Seedmate/Seedmate/SW/src/words_opt.h

#ifndef WORDS_H
#define WORDS_H

const char bip39_words[] =
    "ABANDON\0ABILITY\0ABLE\0ABOUT\0ABOVE\0ABSENT\0ABSORB\0ABSTRACT\0"
    "ABSURD\0ABUSE\0ACCESS\0ACCIDENT\0ACCOUNT\0ACCUSE\0ACHIEVE\0ACID\0"
    "ACOUSTIC\0ACQUIRE\0ACROSS\0ACT\0ACTION\0ACTOR\0ACTRESS\0ACTUAL\0"
    "ADAPT\0ADD\0ADDICT\0ADDRESS\0ADJUST\0ADMIT\0ADULT\0ADVANCE\0"
    "ADVICE\0AEROBIC\0AFFAIR\0AFFORD\0AFRAID\0AGAIN\0AGE\0AGENT\0"
    "AGREE\0AHEAD\0AIM\0AIR\0AIRPORT\0AISLE\0ALARM\0ALBUM\0"
    "ALCOHOL\0ALERT\0ALIEN\0ALL\0ALLEY\0ALLOW\0ALMOST\0ALONE\0"
    "ALPHA\0ALREADY\0ALSO\0ALTER\0ALWAYS\0AMATEUR\0AMAZING\0AMONG\0"
    "AMOUNT\0AMUSED\0ANALYST\0ANCHOR\0ANCIENT\0ANGER\0ANGLE\0ANGRY\0"
    "ANIMAL\0ANKLE\0ANNOUNCE\0ANNUAL\0ANOTHER\0ANSWER\0ANTENNA\0ANTIQUE\0"
    "ANXIETY\0ANY\0APART\0APOLOGY\0APPEAR\0APPLE\0APPROVE\0APRIL\0"
    "ARCH\0ARCTIC\0AREA\0ARENA\0ARGUE\0ARM\0ARMED\0ARMOR\0"
    "ARMY\0AROUND\0ARRANGE\0ARREST\0ARRIVE\0ARROW\0ART\0ARTEFACT\0"
    "ARTIST\0ARTWORK\0ASK\0ASPECT\0ASSAULT\0ASSET\0ASSIST\0ASSUME\0"
    "ASTHMA\0ATHLETE\0ATOM\0ATTACK\0ATTEND\0ATTITUDE\0ATTRACT\0AUCTION\0"
    "AUDIT\0AUGUST\0AUNT\0AUTHOR\0AUTO\0AUTUMN\0AVERAGE\0AVOCADO\0"
    "AVOID\0AWAKE\0AWARE\0AWAY\0AWESOME\0AWFUL\0AWKWARD\0AXIS\0"
    "BABY\0BACHELOR\0BACON\0BADGE\0BAG\0BALANCE\0BALCONY\0BALL\0"
    "BAMBOO\0BANANA\0BANNER\0BAR\0BARELY\0BARGAIN\0BARREL\0BASE\0"
    "BASIC\0BASKET\0BATTLE\0BEACH\0BEAN\0BEAUTY\0BECAUSE\0BECOME\0"
    "BEEF\0BEFORE\0BEGIN\0BEHAVE\0BEHIND\0BELIEVE\0BELOW\0BELT\0"
    "BENCH\0BENEFIT\0BEST\0BETRAY\0BETTER\0BETWEEN\0BEYOND\0BICYCLE\0"
    "BID\0BIKE\0BIND\0BIOLOGY\0BIRD\0BIRTH\0BITTER\0BLACK\0"
    "BLADE\0BLAME\0BLANKET\0BLAST\0BLEAK\0BLESS\0BLIND\0BLOOD\0"
    "BLOSSOM\0BLOUSE\0BLUE\0BLUR\0BLUSH\0BOARD\0BOAT\0BODY\0"
    "BOIL\0BOMB\0BONE\0BONUS\0BOOK\0BOOST\0BORDER\0BORING\0"
    "BORROW\0BOSS\0BOTTOM\0BOUNCE\0BOX\0BOY\0BRACKET\0BRAIN\0"
    "BRAND\0BRASS\0BRAVE\0BREAD\0BREEZE\0BRICK\0BRIDGE\0BRIEF\0"
    "BRIGHT\0BRING\0BRISK\0BROCCOLI\0BROKEN\0BRONZE\0BROOM\0BROTHER\0"
    "BROWN\0BRUSH\0BUBBLE\0BUDDY\0BUDGET\0BUFFALO\0BUILD\0BULB\0"
    "BULK\0BULLET\0BUNDLE\0BUNKER\0BURDEN\0BURGER\0BURST\0BUS\0"
    "BUSINESS\0BUSY\0BUTTER\0BUYER\0BUZZ\0CABBAGE\0CABIN\0CABLE\0"
    "CACTUS\0CAGE\0CAKE\0CALL\0CALM\0CAMERA\0CAMP\0CAN\0"
    "CANAL\0CANCEL\0CANDY\0CANNON\0CANOE\0CANVAS\0CANYON\0CAPABLE\0"
    "CAPITAL\0CAPTAIN\0CAR\0CARBON\0CARD\0CARGO\0CARPET\0CARRY\0"
    "CART\0CASE\0CASH\0CASINO\0CASTLE\0CASUAL\0CAT\0CATALOG\0"
    "CATCH\0CATEGORY\0CATTLE\0CAUGHT\0CAUSE\0CAUTION\0CAVE\0CEILING\0"
    "CELERY\0CEMENT\0CENSUS\0CENTURY\0CEREAL\0CERTAIN\0CHAIR\0CHALK\0"
    "CHAMPION\0CHANGE\0CHAOS\0CHAPTER\0CHARGE\0CHASE\0CHAT\0CHEAP\0"
    "CHECK\0CHEESE\0CHEF\0CHERRY\0CHEST\0CHICKEN\0CHIEF\0CHILD\0"
    "CHIMNEY\0CHOICE\0CHOOSE\0CHRONIC\0CHUCKLE\0CHUNK\0CHURN\0CIGAR\0"
    "CINNAMON\0CIRCLE\0CITIZEN\0CITY\0CIVIL\0CLAIM\0CLAP\0CLARIFY\0"
    "CLAW\0CLAY\0CLEAN\0CLERK\0CLEVER\0CLICK\0CLIENT\0CLIFF\0"
    "CLIMB\0CLINIC\0CLIP\0CLOCK\0CLOG\0CLOSE\0CLOTH\0CLOUD\0"
    "CLOWN\0CLUB\0CLUMP\0CLUSTER\0CLUTCH\0COACH\0COAST\0COCONUT\0"
    "CODE\0COFFEE\0COIL\0COIN\0COLLECT\0COLOR\0COLUMN\0COMBINE\0"
    "COME\0COMFORT\0COMIC\0COMMON\0COMPANY\0CONCERT\0CONDUCT\0CONFIRM\0"
    "CONGRESS\0CONNECT\0CONSIDER\0CONTROL\0CONVINCE\0COOK\0COOL\0COPPER\0"
    "COPY\0CORAL\0CORE\0CORN\0CORRECT\0COST\0COTTON\0COUCH\0"
    "COUNTRY\0COUPLE\0COURSE\0COUSIN\0COVER\0COYOTE\0CRACK\0CRADLE\0"
    "CRAFT\0CRAM\0CRANE\0CRASH\0CRATER\0CRAWL\0CRAZY\0CREAM\0"
    "CREDIT\0CREEK\0CREW\0CRICKET\0CRIME\0CRISP\0CRITIC\0CROP\0"
    "CROSS\0CROUCH\0CROWD\0CRUCIAL\0CRUEL\0CRUISE\0CRUMBLE\0CRUNCH\0"
    "CRUSH\0CRY\0CRYSTAL\0CUBE\0CULTURE\0CUP\0CUPBOARD\0CURIOUS\0"
    "CURRENT\0CURTAIN\0CURVE\0CUSHION\0CUSTOM\0CUTE\0CYCLE\0DAD\0"
    "DAMAGE\0DAMP\0DANCE\0DANGER\0DARING\0DASH\0DAUGHTER\0DAWN\0"
    "DAY\0DEAL\0DEBATE\0DEBRIS\0DECADE\0DECEMBER\0DECIDE\0DECLINE\0"
    "DECORATE\0DECREASE\0DEER\0DEFENSE\0DEFINE\0DEFY\0DEGREE\0DELAY\0"
    "DELIVER\0DEMAND\0DEMISE\0DENIAL\0DENTIST\0DENY\0DEPART\0DEPEND\0"
    "DEPOSIT\0DEPTH\0DEPUTY\0DERIVE\0DESCRIBE\0DESERT\0DESIGN\0DESK\0"
    "DESPAIR\0DESTROY\0DETAIL\0DETECT\0DEVELOP\0DEVICE\0DEVOTE\0DIAGRAM\0"
    "DIAL\0DIAMOND\0DIARY\0DICE\0DIESEL\0DIET\0DIFFER\0DIGITAL\0"
    "DIGNITY\0DILEMMA\0DINNER\0DINOSAUR\0DIRECT\0DIRT\0DISAGREE\0DISCOVER\0"
    "DISEASE\0DISH\0DISMISS\0DISORDER\0DISPLAY\0DISTANCE\0DIVERT\0DIVIDE\0"
    "DIVORCE\0DIZZY\0DOCTOR\0DOCUMENT\0DOG\0DOLL\0DOLPHIN\0DOMAIN\0"
    "DONATE\0DONKEY\0DONOR\0DOOR\0DOSE\0DOUBLE\0DOVE\0DRAFT\0"
    "DRAGON\0DRAMA\0DRASTIC\0DRAW\0DREAM\0DRESS\0DRIFT\0DRILL\0"
    "DRINK\0DRIP\0DRIVE\0DROP\0DRUM\0DRY\0DUCK\0DUMB\0"
    "DUNE\0DURING\0DUST\0DUTCH\0DUTY\0DWARF\0DYNAMIC\0EAGER\0"
    "EAGLE\0EARLY\0EARN\0EARTH\0EASILY\0EAST\0EASY\0ECHO\0"
    "ECOLOGY\0ECONOMY\0EDGE\0EDIT\0EDUCATE\0EFFORT\0EGG\0EIGHT\0"
    "EITHER\0ELBOW\0ELDER\0ELECTRIC\0ELEGANT\0ELEMENT\0ELEPHANT\0ELEVATOR\0"
    "ELITE\0ELSE\0EMBARK\0EMBODY\0EMBRACE\0EMERGE\0EMOTION\0EMPLOY\0"
    "EMPOWER\0EMPTY\0ENABLE\0ENACT\0END\0ENDLESS\0ENDORSE\0ENEMY\0"
    "ENERGY\0ENFORCE\0ENGAGE\0ENGINE\0ENHANCE\0ENJOY\0ENLIST\0ENOUGH\0"
    "ENRICH\0ENROLL\0ENSURE\0ENTER\0ENTIRE\0ENTRY\0ENVELOPE\0EPISODE\0"
    "EQUAL\0EQUIP\0ERA\0ERASE\0ERODE\0EROSION\0ERROR\0ERUPT\0"
    "ESCAPE\0ESSAY\0ESSENCE\0ESTATE\0ETERNAL\0ETHICS\0EVIDENCE\0EVIL\0"
    "EVOKE\0EVOLVE\0EXACT\0EXAMPLE\0EXCESS\0EXCHANGE\0EXCITE\0EXCLUDE\0"
    "EXCUSE\0EXECUTE\0EXERCISE\0EXHAUST\0EXHIBIT\0EXILE\0EXIST\0EXIT\0"
    "EXOTIC\0EXPAND\0EXPECT\0EXPIRE\0EXPLAIN\0EXPOSE\0EXPRESS\0EXTEND\0"
    "EXTRA\0EYE\0EYEBROW\0FABRIC\0FACE\0FACULTY\0FADE\0FAINT\0"
    "FAITH\0FALL\0FALSE\0FAME\0FAMILY\0FAMOUS\0FAN\0FANCY\0"
    "FANTASY\0FARM\0FASHION\0FAT\0FATAL\0FATHER\0FATIGUE\0FAULT\0"
    "FAVORITE\0FEATURE\0FEBRUARY\0FEDERAL\0FEE\0FEED\0FEEL\0FEMALE\0"
    "FENCE\0FESTIVAL\0FETCH\0FEVER\0FEW\0FIBER\0FICTION\0FIELD\0"
    "FIGURE\0FILE\0FILM\0FILTER\0FINAL\0FIND\0FINE\0FINGER\0"
    "FINISH\0FIRE\0FIRM\0FIRST\0FISCAL\0FISH\0FIT\0FITNESS\0"
    "FIX\0FLAG\0FLAME\0FLASH\0FLAT\0FLAVOR\0FLEE\0FLIGHT\0"
    "FLIP\0FLOAT\0FLOCK\0FLOOR\0FLOWER\0FLUID\0FLUSH\0FLY\0"
    "FOAM\0FOCUS\0FOG\0FOIL\0FOLD\0FOLLOW\0FOOD\0FOOT\0"
    "FORCE\0FOREST\0FORGET\0FORK\0FORTUNE\0FORUM\0FORWARD\0FOSSIL\0"
    "FOSTER\0FOUND\0FOX\0FRAGILE\0FRAME\0FREQUENT\0FRESH\0FRIEND\0"
    "FRINGE\0FROG\0FRONT\0FROST\0FROWN\0FROZEN\0FRUIT\0FUEL\0"
    "FUN\0FUNNY\0FURNACE\0FURY\0FUTURE\0GADGET\0GAIN\0GALAXY\0"
    "GALLERY\0GAME\0GAP\0GARAGE\0GARBAGE\0GARDEN\0GARLIC\0GARMENT\0"
    "GAS\0GASP\0GATE\0GATHER\0GAUGE\0GAZE\0GENERAL\0GENIUS\0"
    "GENRE\0GENTLE\0GENUINE\0GESTURE\0GHOST\0GIANT\0GIFT\0GIGGLE\0"
    "GINGER\0GIRAFFE\0GIRL\0GIVE\0GLAD\0GLANCE\0GLARE\0GLASS\0"
    "GLIDE\0GLIMPSE\0GLOBE\0GLOOM\0GLORY\0GLOVE\0GLOW\0GLUE\0"
    "GOAT\0GODDESS\0GOLD\0GOOD\0GOOSE\0GORILLA\0GOSPEL\0GOSSIP\0"
    "GOVERN\0GOWN\0GRAB\0GRACE\0GRAIN\0GRANT\0GRAPE\0GRASS\0"
    "GRAVITY\0GREAT\0GREEN\0GRID\0GRIEF\0GRIT\0GROCERY\0GROUP\0"
    "GROW\0GRUNT\0GUARD\0GUESS\0GUIDE\0GUILT\0GUITAR\0GUN\0"
    "GYM\0HABIT\0HAIR\0HALF\0HAMMER\0HAMSTER\0HAND\0HAPPY\0"
    "HARBOR\0HARD\0HARSH\0HARVEST\0HAT\0HAVE\0HAWK\0HAZARD\0"
    "HEAD\0HEALTH\0HEART\0HEAVY\0HEDGEHOG\0HEIGHT\0HELLO\0HELMET\0"
    "HELP\0HEN\0HERO\0HIDDEN\0HIGH\0HILL\0HINT\0HIP\0"
    "HIRE\0HISTORY\0HOBBY\0HOCKEY\0HOLD\0HOLE\0HOLIDAY\0HOLLOW\0"
    "HOME\0HONEY\0HOOD\0HOPE\0HORN\0HORROR\0HORSE\0HOSPITAL\0"
    "HOST\0HOTEL\0HOUR\0HOVER\0HUB\0HUGE\0HUMAN\0HUMBLE\0"
    "HUMOR\0HUNDRED\0HUNGRY\0HUNT\0HURDLE\0HURRY\0HURT\0HUSBAND\0"
    "HYBRID\0ICE\0ICON\0IDEA\0IDENTIFY\0IDLE\0IGNORE\0ILL\0"
    "ILLEGAL\0ILLNESS\0IMAGE\0IMITATE\0IMMENSE\0IMMUNE\0IMPACT\0IMPOSE\0"
    "IMPROVE\0IMPULSE\0INCH\0INCLUDE\0INCOME\0INCREASE\0INDEX\0INDICATE\0"
    "INDOOR\0INDUSTRY\0INFANT\0INFLICT\0INFORM\0INHALE\0INHERIT\0INITIAL\0"
    "INJECT\0INJURY\0INMATE\0INNER\0INNOCENT\0INPUT\0INQUIRY\0INSANE\0"
    "INSECT\0INSIDE\0INSPIRE\0INSTALL\0INTACT\0INTEREST\0INTO\0INVEST\0"
    "INVITE\0INVOLVE\0IRON\0ISLAND\0ISOLATE\0ISSUE\0ITEM\0IVORY\0"
    "JACKET\0JAGUAR\0JAR\0JAZZ\0JEALOUS\0JEANS\0JELLY\0JEWEL\0"
    "JOB\0JOIN\0JOKE\0JOURNEY\0JOY\0JUDGE\0JUICE\0JUMP\0"
    "JUNGLE\0JUNIOR\0JUNK\0JUST\0KANGAROO\0KEEN\0KEEP\0KETCHUP\0"
    "KEY\0KICK\0KID\0KIDNEY\0KIND\0KINGDOM\0KISS\0KIT\0"
    "KITCHEN\0KITE\0KITTEN\0KIWI\0KNEE\0KNIFE\0KNOCK\0KNOW\0"
    "LAB\0LABEL\0LABOR\0LADDER\0LADY\0LAKE\0LAMP\0LANGUAGE\0"
    "LAPTOP\0LARGE\0LATER\0LATIN\0LAUGH\0LAUNDRY\0LAVA\0LAW\0"
    "LAWN\0LAWSUIT\0LAYER\0LAZY\0LEADER\0LEAF\0LEARN\0LEAVE\0"
    "LECTURE\0LEFT\0LEG\0LEGAL\0LEGEND\0LEISURE\0LEMON\0LEND\0"
    "LENGTH\0LENS\0LEOPARD\0LESSON\0LETTER\0LEVEL\0LIAR\0LIBERTY\0"
    "LIBRARY\0LICENSE\0LIFE\0LIFT\0LIGHT\0LIKE\0LIMB\0LIMIT\0"
    "LINK\0LION\0LIQUID\0LIST\0LITTLE\0LIVE\0LIZARD\0LOAD\0"
    "LOAN\0LOBSTER\0LOCAL\0LOCK\0LOGIC\0LONELY\0LONG\0LOOP\0"
    "LOTTERY\0LOUD\0LOUNGE\0LOVE\0LOYAL\0LUCKY\0LUGGAGE\0LUMBER\0"
    "LUNAR\0LUNCH\0LUXURY\0LYRICS\0MACHINE\0MAD\0MAGIC\0MAGNET\0"
    "MAID\0MAIL\0MAIN\0MAJOR\0MAKE\0MAMMAL\0MAN\0MANAGE\0"
    "MANDATE\0MANGO\0MANSION\0MANUAL\0MAPLE\0MARBLE\0MARCH\0MARGIN\0"
    "MARINE\0MARKET\0MARRIAGE\0MASK\0MASS\0MASTER\0MATCH\0MATERIAL\0"
    "MATH\0MATRIX\0MATTER\0MAXIMUM\0MAZE\0MEADOW\0MEAN\0MEASURE\0"
    "MEAT\0MECHANIC\0MEDAL\0MEDIA\0MELODY\0MELT\0MEMBER\0MEMORY\0"
    "MENTION\0MENU\0MERCY\0MERGE\0MERIT\0MERRY\0MESH\0MESSAGE\0"
    "METAL\0METHOD\0MIDDLE\0MIDNIGHT\0MILK\0MILLION\0MIMIC\0MIND\0"
    "MINIMUM\0MINOR\0MINUTE\0MIRACLE\0MIRROR\0MISERY\0MISS\0MISTAKE\0"
    "MIX\0MIXED\0MIXTURE\0MOBILE\0MODEL\0MODIFY\0MOM\0MOMENT\0"
    "MONITOR\0MONKEY\0MONSTER\0MONTH\0MOON\0MORAL\0MORE\0MORNING\0"
    "MOSQUITO\0MOTHER\0MOTION\0MOTOR\0MOUNTAIN\0MOUSE\0MOVE\0MOVIE\0"
    "MUCH\0MUFFIN\0MULE\0MULTIPLY\0MUSCLE\0MUSEUM\0MUSHROOM\0MUSIC\0"
    "MUST\0MUTUAL\0MYSELF\0MYSTERY\0MYTH\0NAIVE\0NAME\0NAPKIN\0"
    "NARROW\0NASTY\0NATION\0NATURE\0NEAR\0NECK\0NEED\0NEGATIVE\0"
    "NEGLECT\0NEITHER\0NEPHEW\0NERVE\0NEST\0NET\0NETWORK\0NEUTRAL\0"
    "NEVER\0NEWS\0NEXT\0NICE\0NIGHT\0NOBLE\0NOISE\0NOMINEE\0"
    "NOODLE\0NORMAL\0NORTH\0NOSE\0NOTABLE\0NOTE\0NOTHING\0NOTICE\0"
    "NOVEL\0NOW\0NUCLEAR\0NUMBER\0NURSE\0NUT\0OAK\0OBEY\0"
    "OBJECT\0OBLIGE\0OBSCURE\0OBSERVE\0OBTAIN\0OBVIOUS\0OCCUR\0OCEAN\0"
    "OCTOBER\0ODOR\0OFF\0OFFER\0OFFICE\0OFTEN\0OIL\0OKAY\0"
    "OLD\0OLIVE\0OLYMPIC\0OMIT\0ONCE\0ONE\0ONION\0ONLINE\0"
    "ONLY\0OPEN\0OPERA\0OPINION\0OPPOSE\0OPTION\0ORANGE\0ORBIT\0"
    "ORCHARD\0ORDER\0ORDINARY\0ORGAN\0ORIENT\0ORIGINAL\0ORPHAN\0OSTRICH\0"
    "OTHER\0OUTDOOR\0OUTER\0OUTPUT\0OUTSIDE\0OVAL\0OVEN\0OVER\0"
    "OWN\0OWNER\0OXYGEN\0OYSTER\0OZONE\0PACT\0PADDLE\0PAGE\0"
    "PAIR\0PALACE\0PALM\0PANDA\0PANEL\0PANIC\0PANTHER\0PAPER\0"
    "PARADE\0PARENT\0PARK\0PARROT\0PARTY\0PASS\0PATCH\0PATH\0"
    "PATIENT\0PATROL\0PATTERN\0PAUSE\0PAVE\0PAYMENT\0PEACE\0PEANUT\0"
    "PEAR\0PEASANT\0PELICAN\0PEN\0PENALTY\0PENCIL\0PEOPLE\0PEPPER\0"
    "PERFECT\0PERMIT\0PERSON\0PET\0PHONE\0PHOTO\0PHRASE\0PHYSICAL\0"
    "PIANO\0PICNIC\0PICTURE\0PIECE\0PIG\0PIGEON\0PILL\0PILOT\0"
    "PINK\0PIONEER\0PIPE\0PISTOL\0PITCH\0PIZZA\0PLACE\0PLANET\0"
    "PLASTIC\0PLATE\0PLAY\0PLEASE\0PLEDGE\0PLUCK\0PLUG\0PLUNGE\0"
    "POEM\0POET\0POINT\0POLAR\0POLE\0POLICE\0POND\0PONY\0"
    "POOL\0POPULAR\0PORTION\0POSITION\0POSSIBLE\0POST\0POTATO\0POTTERY\0"
    "POVERTY\0POWDER\0POWER\0PRACTICE\0PRAISE\0PREDICT\0PREFER\0PREPARE\0"
    "PRESENT\0PRETTY\0PREVENT\0PRICE\0PRIDE\0PRIMARY\0PRINT\0PRIORITY\0"
    "PRISON\0PRIVATE\0PRIZE\0PROBLEM\0PROCESS\0PRODUCE\0PROFIT\0PROGRAM\0"
    "PROJECT\0PROMOTE\0PROOF\0PROPERTY\0PROSPER\0PROTECT\0PROUD\0PROVIDE\0"
    "PUBLIC\0PUDDING\0PULL\0PULP\0PULSE\0PUMPKIN\0PUNCH\0PUPIL\0"
    "PUPPY\0PURCHASE\0PURITY\0PURPOSE\0PURSE\0PUSH\0PUT\0PUZZLE\0"
    "PYRAMID\0QUALITY\0QUANTUM\0QUARTER\0QUESTION\0QUICK\0QUIT\0QUIZ\0"
    "QUOTE\0RABBIT\0RACCOON\0RACE\0RACK\0RADAR\0RADIO\0RAIL\0"
    "RAIN\0RAISE\0RALLY\0RAMP\0RANCH\0RANDOM\0RANGE\0RAPID\0"
    "RARE\0RATE\0RATHER\0RAVEN\0RAW\0RAZOR\0READY\0REAL\0"
    "REASON\0REBEL\0REBUILD\0RECALL\0RECEIVE\0RECIPE\0RECORD\0RECYCLE\0"
    "REDUCE\0REFLECT\0REFORM\0REFUSE\0REGION\0REGRET\0REGULAR\0REJECT\0"
    "RELAX\0RELEASE\0RELIEF\0RELY\0REMAIN\0REMEMBER\0REMIND\0REMOVE\0"
    "RENDER\0RENEW\0RENT\0REOPEN\0REPAIR\0REPEAT\0REPLACE\0REPORT\0"
    "REQUIRE\0RESCUE\0RESEMBLE\0RESIST\0RESOURCE\0RESPONSE\0RESULT\0RETIRE\0"
    "RETREAT\0RETURN\0REUNION\0REVEAL\0REVIEW\0REWARD\0RHYTHM\0RIB\0"
    "RIBBON\0RICE\0RICH\0RIDE\0RIDGE\0RIFLE\0RIGHT\0RIGID\0"
    "RING\0RIOT\0RIPPLE\0RISK\0RITUAL\0RIVAL\0RIVER\0ROAD\0"
    "ROAST\0ROBOT\0ROBUST\0ROCKET\0ROMANCE\0ROOF\0ROOKIE\0ROOM\0"
    "ROSE\0ROTATE\0ROUGH\0ROUND\0ROUTE\0ROYAL\0RUBBER\0RUDE\0"
    "RUG\0RULE\0RUN\0RUNWAY\0RURAL\0SAD\0SADDLE\0SADNESS\0"
    "SAFE\0SAIL\0SALAD\0SALMON\0SALON\0SALT\0SALUTE\0SAME\0"
    "SAMPLE\0SAND\0SATISFY\0SATOSHI\0SAUCE\0SAUSAGE\0SAVE\0SAY\0"
    "SCALE\0SCAN\0SCARE\0SCATTER\0SCENE\0SCHEME\0SCHOOL\0SCIENCE\0"
    "SCISSORS\0SCORPION\0SCOUT\0SCRAP\0SCREEN\0SCRIPT\0SCRUB\0SEA\0"
    "SEARCH\0SEASON\0SEAT\0SECOND\0SECRET\0SECTION\0SECURITY\0SEED\0"
    "SEEK\0SEGMENT\0SELECT\0SELL\0SEMINAR\0SENIOR\0SENSE\0SENTENCE\0"
    "SERIES\0SERVICE\0SESSION\0SETTLE\0SETUP\0SEVEN\0SHADOW\0SHAFT\0"
    "SHALLOW\0SHARE\0SHED\0SHELL\0SHERIFF\0SHIELD\0SHIFT\0SHINE\0"
    "SHIP\0SHIVER\0SHOCK\0SHOE\0SHOOT\0SHOP\0SHORT\0SHOULDER\0"
    "SHOVE\0SHRIMP\0SHRUG\0SHUFFLE\0SHY\0SIBLING\0SICK\0SIDE\0"
    "SIEGE\0SIGHT\0SIGN\0SILENT\0SILK\0SILLY\0SILVER\0SIMILAR\0"
    "SIMPLE\0SINCE\0SING\0SIREN\0SISTER\0SITUATE\0SIX\0SIZE\0"
    "SKATE\0SKETCH\0SKI\0SKILL\0SKIN\0SKIRT\0SKULL\0SLAB\0"
    "SLAM\0SLEEP\0SLENDER\0SLICE\0SLIDE\0SLIGHT\0SLIM\0SLOGAN\0"
    "SLOT\0SLOW\0SLUSH\0SMALL\0SMART\0SMILE\0SMOKE\0SMOOTH\0"
    "SNACK\0SNAKE\0SNAP\0SNIFF\0SNOW\0SOAP\0SOCCER\0SOCIAL\0"
    "SOCK\0SODA\0SOFT\0SOLAR\0SOLDIER\0SOLID\0SOLUTION\0SOLVE\0"
    "SOMEONE\0SONG\0SOON\0SORRY\0SORT\0SOUL\0SOUND\0SOUP\0"
    "SOURCE\0SOUTH\0SPACE\0SPARE\0SPATIAL\0SPAWN\0SPEAK\0SPECIAL\0"
    "SPEED\0SPELL\0SPEND\0SPHERE\0SPICE\0SPIDER\0SPIKE\0SPIN\0"
    "SPIRIT\0SPLIT\0SPOIL\0SPONSOR\0SPOON\0SPORT\0SPOT\0SPRAY\0"
    "SPREAD\0SPRING\0SPY\0SQUARE\0SQUEEZE\0SQUIRREL\0STABLE\0STADIUM\0"
    "STAFF\0STAGE\0STAIRS\0STAMP\0STAND\0START\0STATE\0STAY\0"
    "STEAK\0STEEL\0STEM\0STEP\0STEREO\0STICK\0STILL\0STING\0"
    "STOCK\0STOMACH\0STONE\0STOOL\0STORY\0STOVE\0STRATEGY\0STREET\0"
    "STRIKE\0STRONG\0STRUGGLE\0STUDENT\0STUFF\0STUMBLE\0STYLE\0SUBJECT\0"
    "SUBMIT\0SUBWAY\0SUCCESS\0SUCH\0SUDDEN\0SUFFER\0SUGAR\0SUGGEST\0"
    "SUIT\0SUMMER\0SUN\0SUNNY\0SUNSET\0SUPER\0SUPPLY\0SUPREME\0"
    "SURE\0SURFACE\0SURGE\0SURPRISE\0SURROUND\0SURVEY\0SUSPECT\0SUSTAIN\0"
    "SWALLOW\0SWAMP\0SWAP\0SWARM\0SWEAR\0SWEET\0SWIFT\0SWIM\0"
    "SWING\0SWITCH\0SWORD\0SYMBOL\0SYMPTOM\0SYRUP\0SYSTEM\0TABLE\0"
    "TACKLE\0TAG\0TAIL\0TALENT\0TALK\0TANK\0TAPE\0TARGET\0"
    "TASK\0TASTE\0TATTOO\0TAXI\0TEACH\0TEAM\0TELL\0TEN\0"
    "TENANT\0TENNIS\0TENT\0TERM\0TEST\0TEXT\0THANK\0THAT\0"
    "THEME\0THEN\0THEORY\0THERE\0THEY\0THING\0THIS\0THOUGHT\0"
    "THREE\0THRIVE\0THROW\0THUMB\0THUNDER\0TICKET\0TIDE\0TIGER\0"
    "TILT\0TIMBER\0TIME\0TINY\0TIP\0TIRED\0TISSUE\0TITLE\0"
    "TOAST\0TOBACCO\0TODAY\0TODDLER\0TOE\0TOGETHER\0TOILET\0TOKEN\0"
    "TOMATO\0TOMORROW\0TONE\0TONGUE\0TONIGHT\0TOOL\0TOOTH\0TOP\0"
    "TOPIC\0TOPPLE\0TORCH\0TORNADO\0TORTOISE\0TOSS\0TOTAL\0TOURIST\0"
    "TOWARD\0TOWER\0TOWN\0TOY\0TRACK\0TRADE\0TRAFFIC\0TRAGIC\0"
    "TRAIN\0TRANSFER\0TRAP\0TRASH\0TRAVEL\0TRAY\0TREAT\0TREE\0"
    "TREND\0TRIAL\0TRIBE\0TRICK\0TRIGGER\0TRIM\0TRIP\0TROPHY\0"
    "TROUBLE\0TRUCK\0TRUE\0TRULY\0TRUMPET\0TRUST\0TRUTH\0TRY\0"
    "TUBE\0TUITION\0TUMBLE\0TUNA\0TUNNEL\0TURKEY\0TURN\0TURTLE\0"
    "TWELVE\0TWENTY\0TWICE\0TWIN\0TWIST\0TWO\0TYPE\0TYPICAL\0"
    "UGLY\0UMBRELLA\0UNABLE\0UNAWARE\0UNCLE\0UNCOVER\0UNDER\0UNDO\0"
    "UNFAIR\0UNFOLD\0UNHAPPY\0UNIFORM\0UNIQUE\0UNIT\0UNIVERSE\0UNKNOWN\0"
    "UNLOCK\0UNTIL\0UNUSUAL\0UNVEIL\0UPDATE\0UPGRADE\0UPHOLD\0UPON\0"
    "UPPER\0UPSET\0URBAN\0URGE\0USAGE\0USE\0USED\0USEFUL\0"
    "USELESS\0USUAL\0UTILITY\0VACANT\0VACUUM\0VAGUE\0VALID\0VALLEY\0"
    "VALVE\0VAN\0VANISH\0VAPOR\0VARIOUS\0VAST\0VAULT\0VEHICLE\0"
    "VELVET\0VENDOR\0VENTURE\0VENUE\0VERB\0VERIFY\0VERSION\0VERY\0"
    "VESSEL\0VETERAN\0VIABLE\0VIBRANT\0VICIOUS\0VICTORY\0VIDEO\0VIEW\0"
    "VILLAGE\0VINTAGE\0VIOLIN\0VIRTUAL\0VIRUS\0VISA\0VISIT\0VISUAL\0"
    "VITAL\0VIVID\0VOCAL\0VOICE\0VOID\0VOLCANO\0VOLUME\0VOTE\0"
    "VOYAGE\0WAGE\0WAGON\0WAIT\0WALK\0WALL\0WALNUT\0WANT\0"
    "WARFARE\0WARM\0WARRIOR\0WASH\0WASP\0WASTE\0WATER\0WAVE\0"
    "WAY\0WEALTH\0WEAPON\0WEAR\0WEASEL\0WEATHER\0WEB\0WEDDING\0"
    "WEEKEND\0WEIRD\0WELCOME\0WEST\0WET\0WHALE\0WHAT\0WHEAT\0"
    "WHEEL\0WHEN\0WHERE\0WHIP\0WHISPER\0WIDE\0WIDTH\0WIFE\0"
    "WILD\0WILL\0WIN\0WINDOW\0WINE\0WING\0WINK\0WINNER\0"
    "WINTER\0WIRE\0WISDOM\0WISE\0WISH\0WITNESS\0WOLF\0WOMAN\0"
    "WONDER\0WOOD\0WOOL\0WORD\0WORK\0WORLD\0WORRY\0WORTH\0"
    "WRAP\0WRECK\0WRESTLE\0WRIST\0WRITE\0WRONG\0YARD\0YEAR\0"
    "YELLOW\0YOU\0YOUNG\0YOUTH\0ZEBRA\0ZERO\0ZONE\0ZOO\0"
;

#endif // WORDS_H
