Seedmate/Seedmate/SW/src/config/default/peripheral/evic/plib_evic.c

/*******************************************************************************
  EVIC PLIB Implementation

  Company:
    Microchip Technology Inc.

  File Name:
    plib_evic.c

  Summary:
    EVIC PLIB Source File

  Description:
    None

*******************************************************************************/

// DOM-IGNORE-BEGIN
/*******************************************************************************
* Copyright (C) 2019 Microchip Technology Inc. and its subsidiaries.
*
* Subject to your compliance with these terms, you may use Microchip software
* and any derivatives exclusively with Microchip products. It is your
* responsibility to comply with third party license terms applicable to your
* use of third party software (including open source software) that may
* accompany Microchip software.
*
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
* IN NO EVENT WILL MICROCHIP BE LIABLE FOR ANY INDIRECT, SPECIAL, PUNITIVE,
* INCIDENTAL OR CONSEQUENTIAL LOSS, DAMAGE, COST OR EXPENSE OF ANY KIND
* WHATSOEVER RELATED TO THE SOFTWARE, HOWEVER CAUSED, EVEN IF MICROCHIP HAS
* BEEN ADVISED OF THE POSSIBILITY OR THE DAMAGES ARE FORESEEABLE. TO THE
* FULLEST EXTENT ALLOWED BY LAW, MICROCHIP'S TOTAL LIABILITY ON ALL CLAIMS IN
* ANY WAY RELATED TO THIS SOFTWARE WILL NOT EXCEED THE AMOUNT OF FEES, IF ANY,
* THAT YOU HAVE PAID DIRECTLY TO MICROCHIP FOR THIS SOFTWARE.
*******************************************************************************/
// DOM-IGNORE-END

#include "device.h"
#include "plib_evic.h"
#include "interrupts.h"


// *****************************************************************************
// *****************************************************************************
// Section: IRQ Implementation
// *****************************************************************************
// *****************************************************************************

void EVIC_Initialize( void )
{
    INTCONSET = _INTCON_MVEC_MASK;

    /* Set up priority and subpriority of enabled interrupts */
    IPC5SET = 0x400U | 0x0U;  /* SPI1_TX:  Priority 1 / Subpriority 0 */



    /* Configure Shadow Register Set */
    PRISS = 0x10000000;

    while (PRISS != 0x10000000U)
    {
        /* Wait for PRISS value to take effect */
    }
}

void EVIC_SourceEnable( INT_SOURCE source )
{
    volatile uint32_t *IECx = (volatile uint32_t *) (&IEC0 + ((0x10U * (source / 32U)) / 4U));
    volatile uint32_t *IECxSET = (volatile uint32_t *)(IECx + 2U);

    *IECxSET = 1UL << (source & 0x1fU);
}

void EVIC_SourceDisable( INT_SOURCE source )
{
    volatile uint32_t *IECx = (volatile uint32_t *) (&IEC0 + ((0x10U * (source / 32U)) / 4U));
    volatile uint32_t *IECxCLR = (volatile uint32_t *)(IECx + 1U);

    *IECxCLR = 1UL << (source & 0x1fU);
}

bool EVIC_SourceIsEnabled( INT_SOURCE source )
{
    volatile uint32_t *IECx = (volatile uint32_t *) (&IEC0 + ((0x10U * (source / 32U)) / 4U));

    return (((*IECx >> (source & 0x1fU)) & 0x01U) != 0U);
}

bool EVIC_SourceStatusGet( INT_SOURCE source )
{
    volatile uint32_t *IFSx = (volatile uint32_t *)(&IFS0 + ((0x10U * (source / 32U)) / 4U));

    return (((*IFSx >> (source & 0x1fU)) & 0x1U) != 0U);
}

void EVIC_SourceStatusSet( INT_SOURCE source )
{
    volatile uint32_t *IFSx = (volatile uint32_t *) (&IFS0 + ((0x10U * (source / 32U)) / 4U));
    volatile uint32_t *IFSxSET = (volatile uint32_t *)(IFSx + 2U);

    *IFSxSET = 1UL << (source & 0x1fU);
}

void EVIC_SourceStatusClear( INT_SOURCE source )
{
    volatile uint32_t *IFSx = (volatile uint32_t *) (&IFS0 + ((0x10U * (source / 32U)) / 4U));
    volatile uint32_t *IFSxCLR = (volatile uint32_t *)(IFSx + 1U);

    *IFSxCLR = 1UL << (source & 0x1fU);
}

void EVIC_INT_Enable( void )
{
   (void) __builtin_enable_interrupts();
}

bool EVIC_INT_Disable( void )
{
    uint32_t processorStatus;

    /* Save the processor status and then Disable the global interrupt */
    processorStatus = ( uint32_t )__builtin_disable_interrupts();

    /* return the interrupt status */
    return ((processorStatus & 0x01U) != 0U);
}

void EVIC_INT_Restore( bool state )
{
    if (state)
    {
        /* restore the state of CP0 Status register before the disable occurred */
       (void) __builtin_enable_interrupts();
    }
}

bool EVIC_INT_SourceDisable( INT_SOURCE source )
{
    bool processorStatus;
    bool intSrcStatus;

    processorStatus = EVIC_INT_Disable();
    intSrcStatus = (EVIC_SourceIsEnabled(source) != 0U);
    EVIC_SourceDisable( source );
    EVIC_INT_Restore( processorStatus );

    /* return the source status */
    return intSrcStatus;
}

void EVIC_INT_SourceRestore( INT_SOURCE source, bool status )
{
    if( status ) {
       EVIC_SourceEnable( source );
    }

    return;
}


/* End of file */
